Drc3p0/Glow-Club-Pathlighter-Badge/images/Glowbug PCB front.jpeg

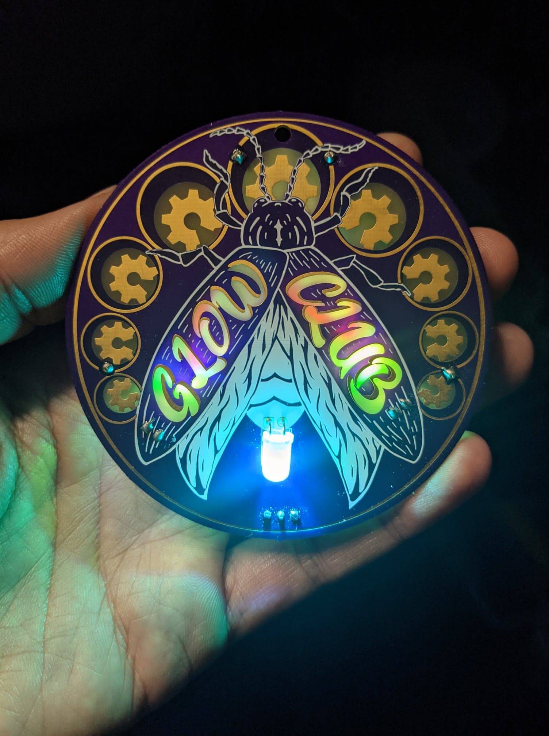
images/Glowbug PCB front.jpeg
