Drc3p0/Glow-Club-Pathlighter-Badge/images/glowbug pcbs.jpg

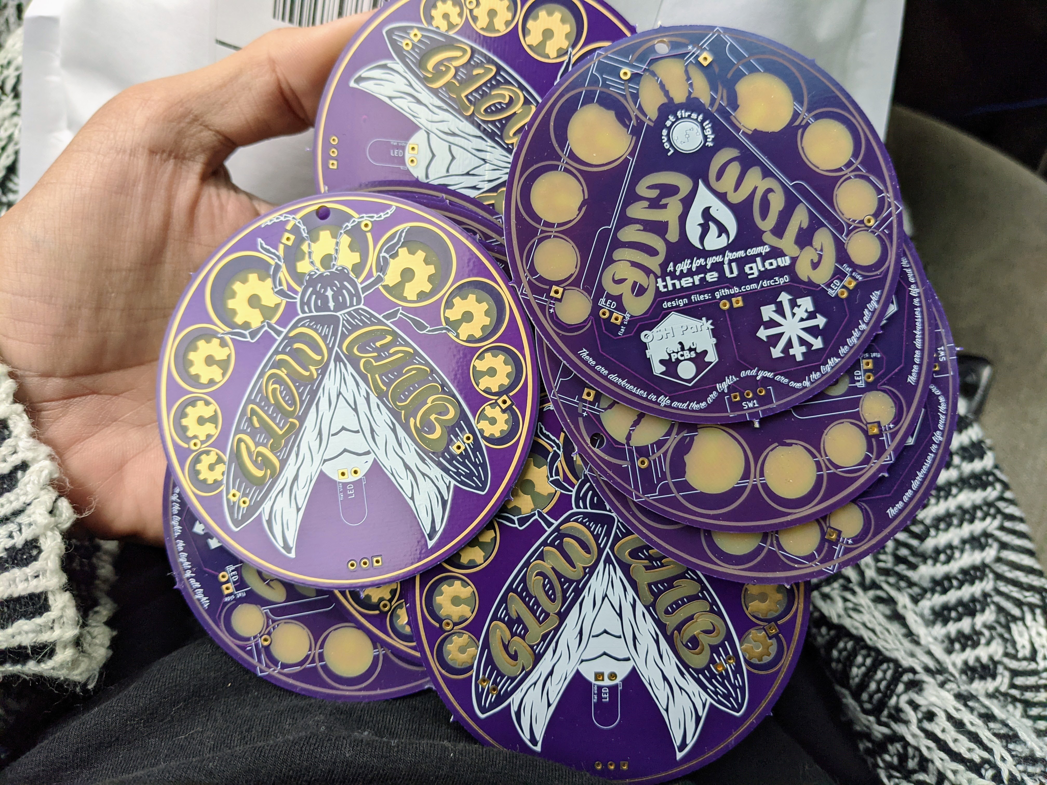
images/glowbug pcbs.jpg
