Drc3p0/Glow-Club-Pathlighter-Badge/images/PCB assembly.jpg

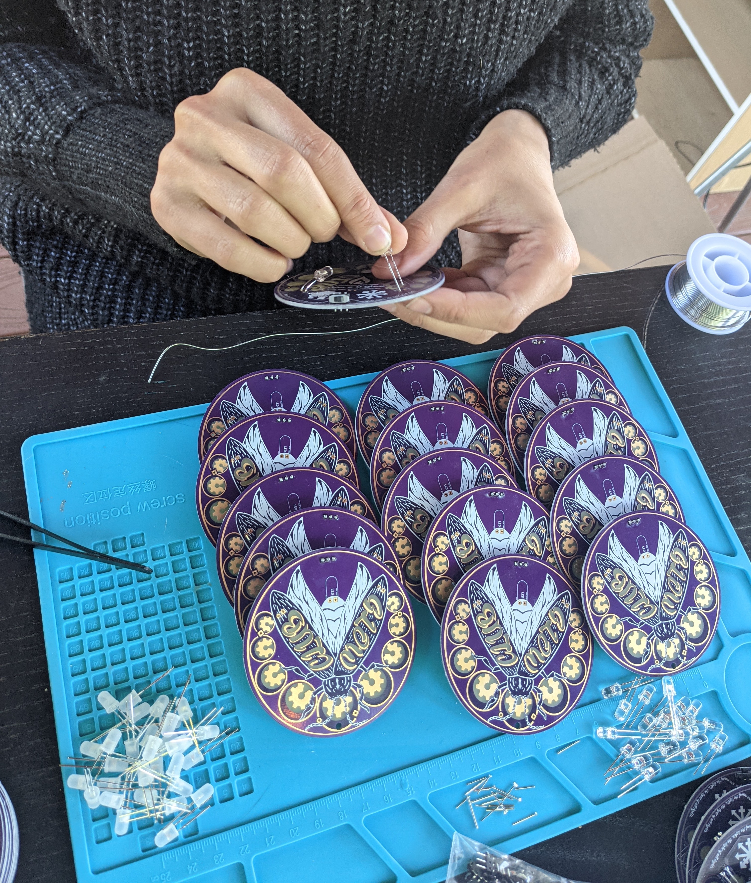
images/PCB assembly.jpg
