Drc3p0/Glow-Club-Pathlighter-Badge/images/soldering-at-CCC23.jpg

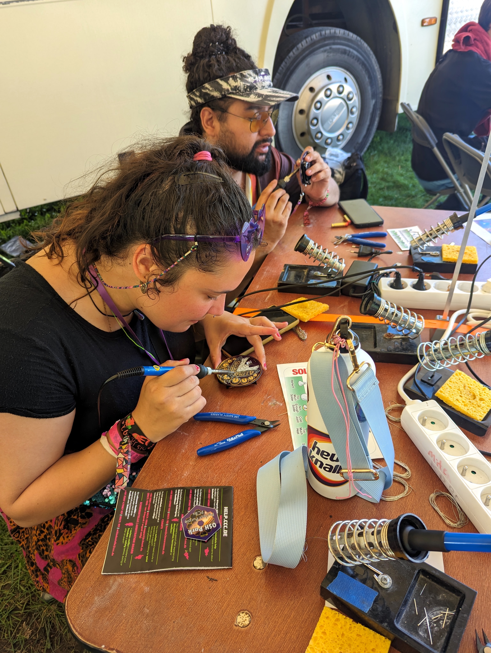
images/soldering-at-CCC23.jpg
